mschyllander/mirror-onoff/firmware/esp_12V_mirror_timer/DeviceConfig.example.h

#pragma once
// Copy to DeviceConfig.h (gitignored). Choose your own passwords.
// Web admin password and direct Wi-Fi password are independent.
#define MIRROR_ADMIN_PASSWORD ""
// WPA2 requires 8-63 characters for the direct Mirror-Setup network.
#define MIRROR_AP_PASSWORD ""
